jernejp21/VoiceNavi/Hardware/Rev1/Audio Prj.pdf

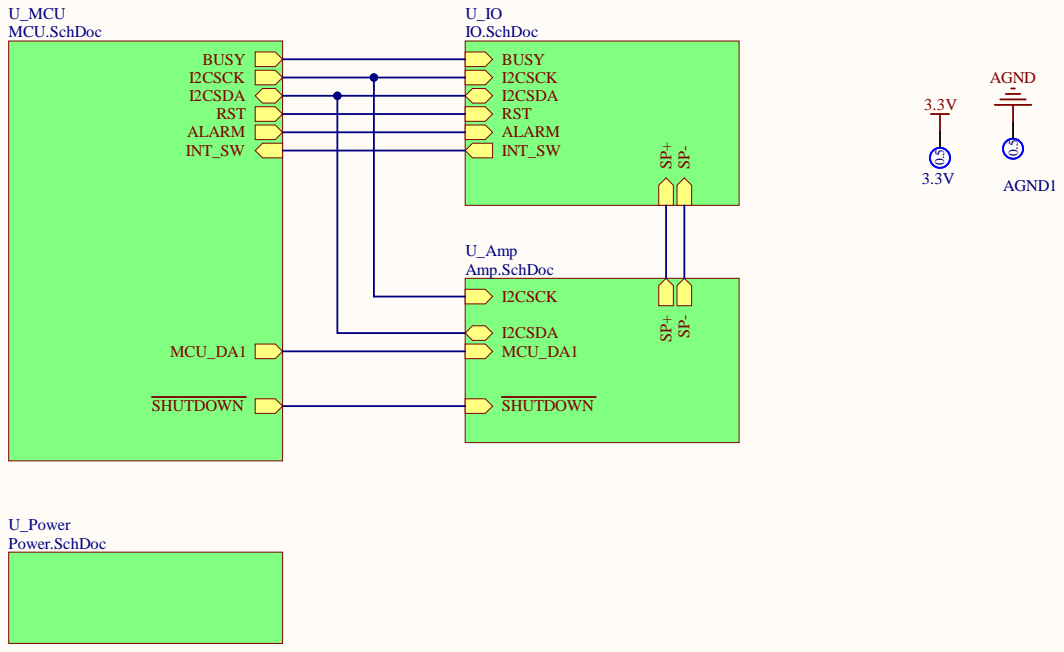
[picture p9: page 1]

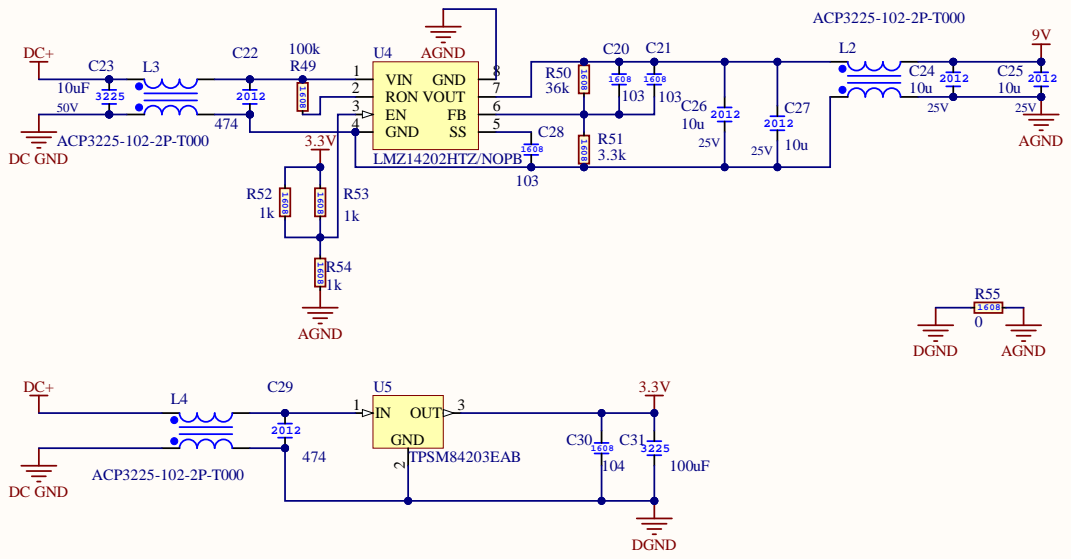
[picture p10: page 2]

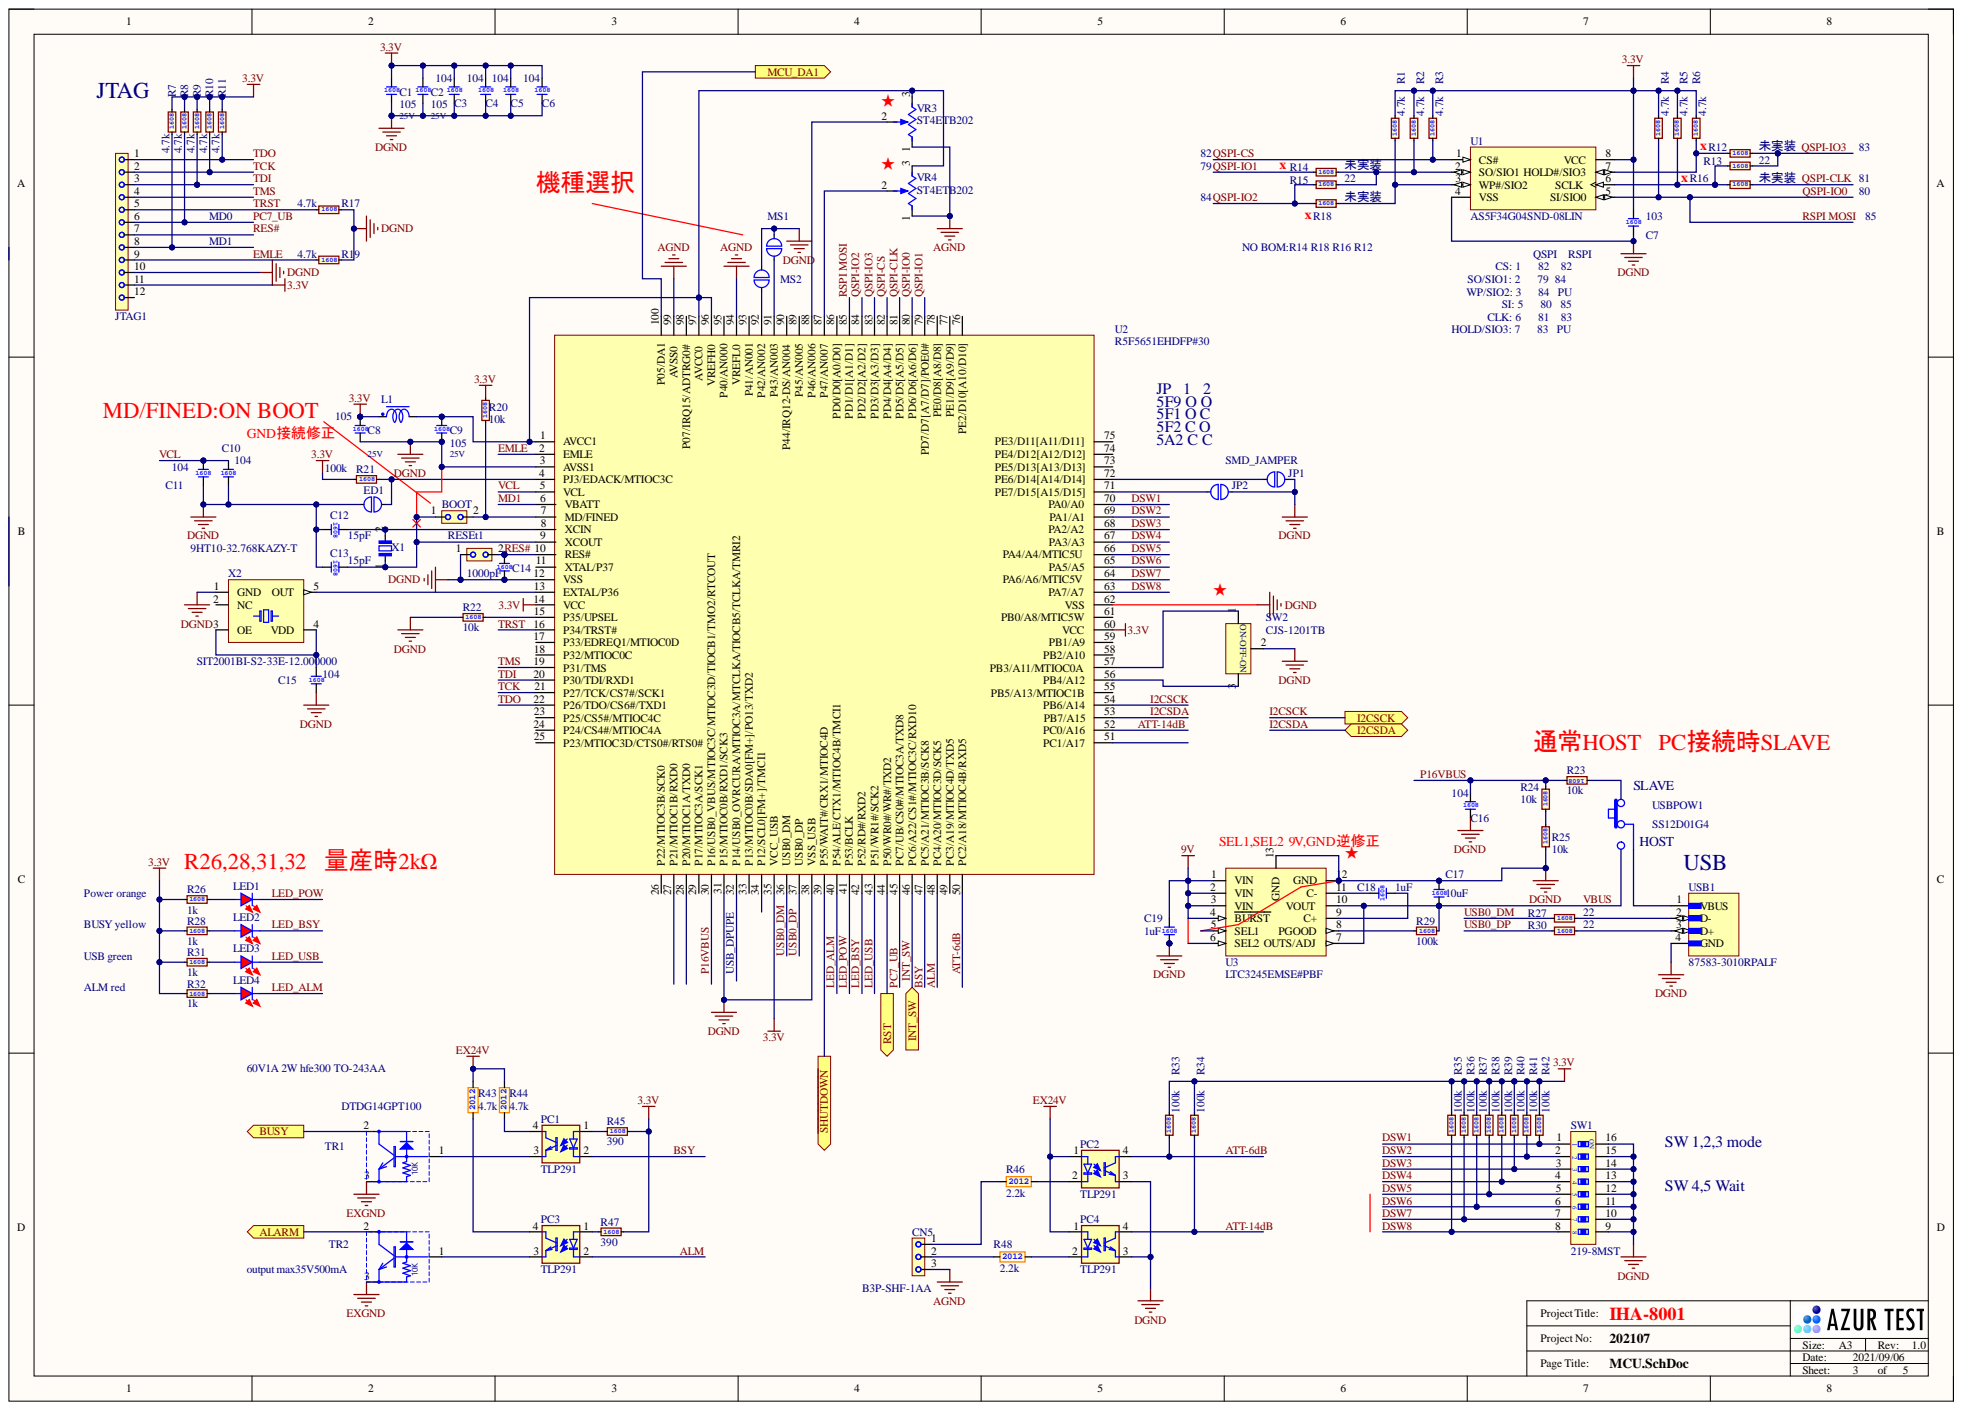
[picture p11: page 3]

MD/FINED:ON BOOT

EMLE | EMLE 2

AVCC1 1

RESEt1 | XCOUT 9
1 | | 2 RES# | RES# 10

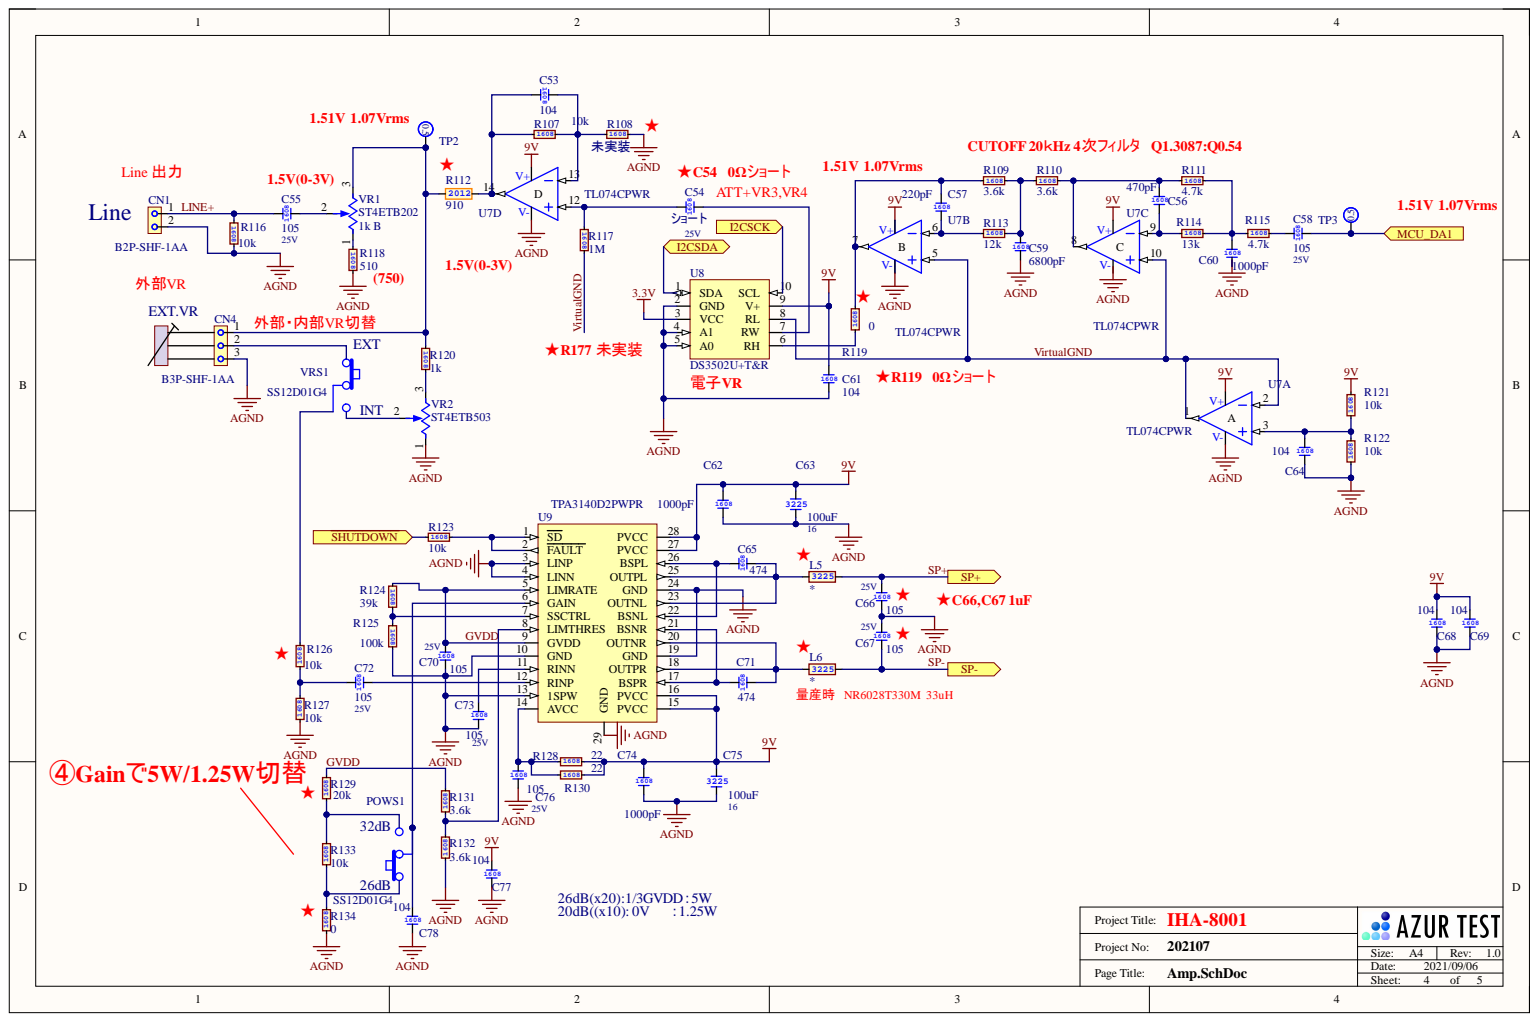
[picture p12: page 4]

SDA 1 | RL
VCC 3 | 8 V+ 9

25V1608 C70 | | LIMTHRES 8

GND 10 | | C71
RINN 11
RINP 12

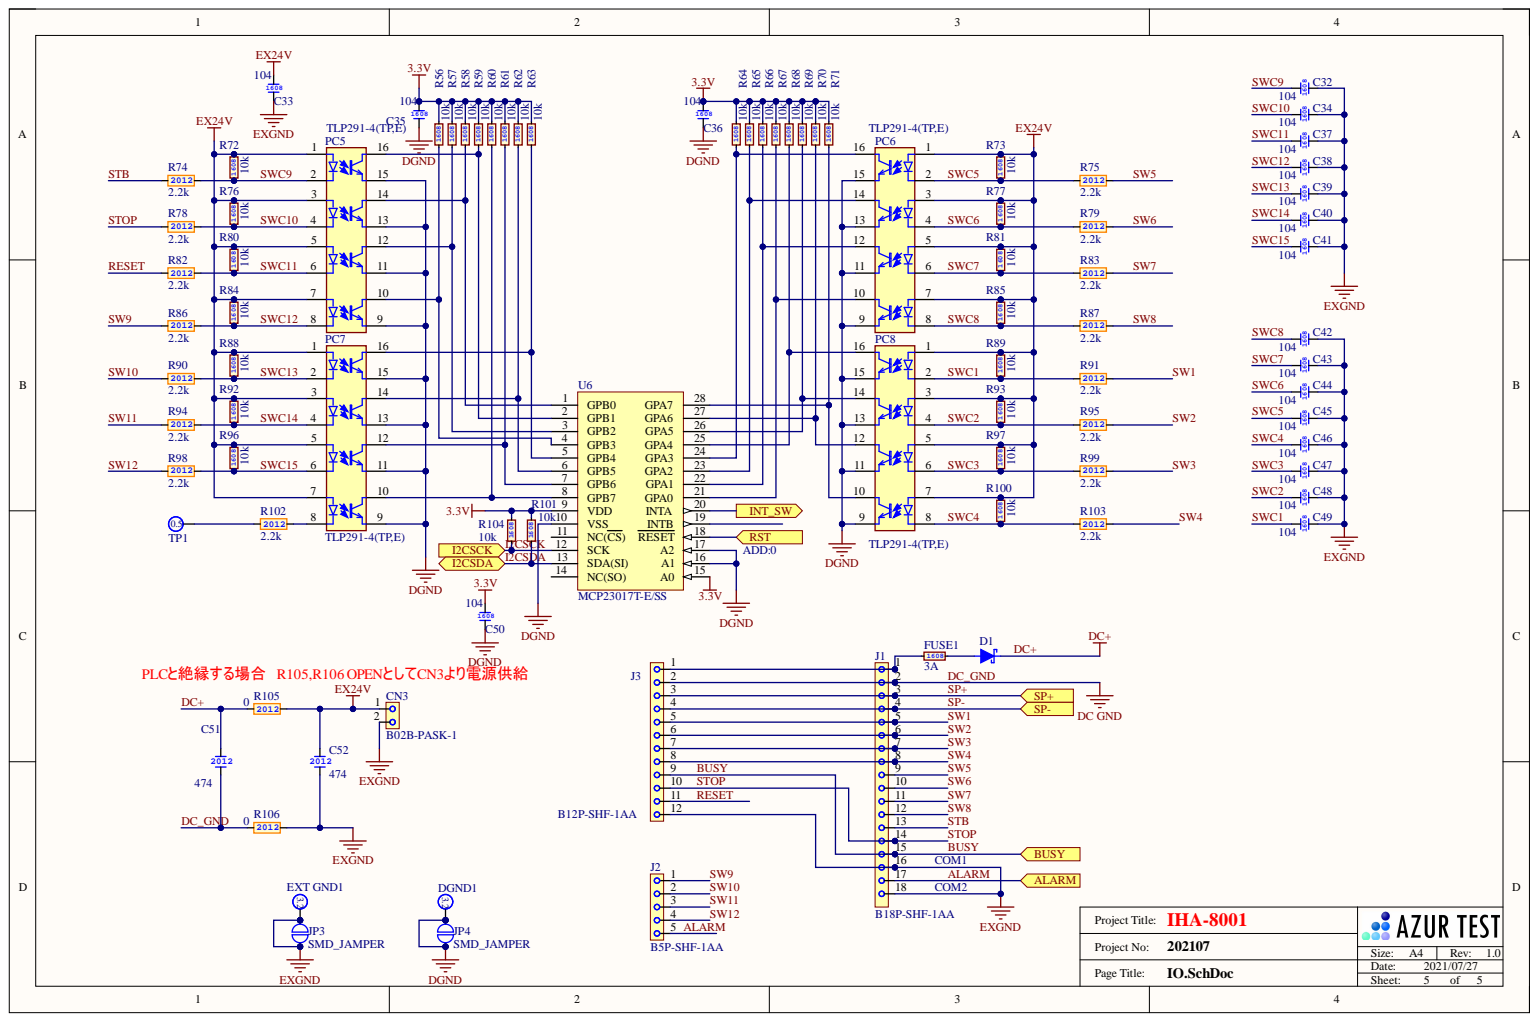
[picture p13: page 5]

3 | 3 SP+
9 BUSY
10 STOP | 10 SW6 BUSY
11 RESET | 11
