jernejp21/VoiceNavi/VoiceNavi/src/smc_gen/PORT_config/PORT_config_user.c

/*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
* Copyright (C) 2019 Renesas Electronics Corporation. All rights reserved.
***********************************************************************************************************************/

/***********************************************************************************************************************
* File Name        : PORT_config_user.c
* Component Version: 2.3.0
* Device(s)        : R5F565N9FxFP
* Description      : This file implements device driver for PORT_config.
***********************************************************************************************************************/

/***********************************************************************************************************************
Pragma directive
***********************************************************************************************************************/
/* Start user code for pragma. Do not edit comment generated here */
/* End user code. Do not edit comment generated here */

/***********************************************************************************************************************
Includes
***********************************************************************************************************************/
#include "r_cg_macrodriver.h"
#include "PORT_config.h"
/* Start user code for include. Do not edit comment generated here */
#include "globals.h"
/* End user code. Do not edit comment generated here */
#include "r_cg_userdefine.h"

/***********************************************************************************************************************
Global variables and functions
***********************************************************************************************************************/
/* Start user code for global. Do not edit comment generated here */
/* End user code. Do not edit comment generated here */

/***********************************************************************************************************************
* Function Name: R_PORT_config_Create_UserInit
* Description  : This function adds user code after initializing PORT
* Arguments    : None
* Return Value : None
***********************************************************************************************************************/

void R_PORT_config_Create_UserInit(void)
{
    /* Start user code for user init. Do not edit comment generated here */
  LED_PowOff();
  LED_BusyOff();
  LED_USBOff();
  LED_AlarmOff();
  PIN_BusySet();
  PIN_AlarmSet();
    /* End user code. Do not edit comment generated here */
}

/* Start user code for adding. Do not edit comment generated here */
void LED_BusyOn()
{
  PORT5.PODR.BIT.B2 = 0;
}

void LED_BusyOff()
{
  PORT5.PODR.BIT.B2 = 1;
}

void LED_BusyToggle()
{
  PORT5.PODR.BIT.B2 ^= 1;
}

void LED_PowOn()
{
  PORT5.PODR.BIT.B3 = 0;
}

void LED_PowOff()
{
  PORT5.PODR.BIT.B3 = 1;
}

void LED_USBOn()
{
  PORT5.PODR.BIT.B1 = 0;
}

void LED_USBOff()
{
  PORT5.PODR.BIT.B1 = 1;
}

void LED_USBToggle()
{
  PORT5.PODR.BIT.B1 ^= 1;
}

void LED_AlarmOn()
{
  PORT5.PODR.BIT.B4 = 0;
}

void LED_AlarmOff()
{
  PORT5.PODR.BIT.B4 = 1;
}

void LED_AlarmToggle()
{
  PORT5.PODR.BIT.B4 ^= 1;
}

uint8_t DIP_ReadState()
{
  //Negative logic, chage to positive.
  return (PORTA.PIDR.BYTE ^ 0xFF);
}

modeSelect_t PIN_BoardSelection()
{
  modeSelect_t ret;
  ret = PORT4.PIDR.BIT.B3; //MS2
  ret |= (PORT4.PIDR.BIT.B2 << 1); //MS1

  return ret;
}

void PIN_ShutdownSet()
{
  PORT5.PODR.BIT.B5 = 1;
}

void PIN_ShutdownReset()
{
  PORT5.PODR.BIT.B5 = 0;
}

void PIN_RstSet()
{
  PORT5.PODR.BIT.B0 = 1;
}

void PIN_RstReset()
{
  PORT5.PODR.BIT.B0 = 0;
}

void PIN_BusySet()
{
  PORTC.PODR.BIT.B5 = 1;
}

void PIN_BusyReset()
{
  PORTC.PODR.BIT.B5 = 0;
}

void PIN_AlarmSet()
{
  PORTC.PODR.BIT.B4 = 1;
}

void PIN_AlarmReset()
{
  PORTC.PODR.BIT.B4 = 0;
}

uint8_t PIN_Get6dB()
{
  return PORTC.PIDR.BIT.B2;
}

uint8_t PIN_Get14dB()
{
  return PORTC.PIDR.BIT.B0;
}

uint8_t PIN_GetExtIRQ()
{
  return PORTC.PIDR.BIT.B6;
}

uint8_t PIN_GetSW2()
{
  // When switch is in middle position, pin status is HIGH.
  // When switch is in voice position, PB3 is LOW.
  // When switch is in chime position, PB4 is LOW.
  // XOR bits to get positive logic - if voice (pos 3), result is 1; if chime (pos 1), result is 2
  uint8_t port = ((PORTB.PIDR.BIT.B4 << 1) | PORTB.PIDR.BIT.B3) ^ 3;
  return port;
}

uint8_t PIN_GetDebugMode()
{
  return PORTE.PIDR.BIT.B6;
}

/* End user code. Do not edit comment generated here */
