jernejp21/VoiceNavi/VoiceNavi/src/play_modes.c

/**
 * Voice Navi Firmware
 *
 * MIT License
 *
 * Copyright (c) 2022 Azurtest
 *
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
 * THE SOFTWARE IS PROVIDED "AS IS", WITHOUT WARRANTY OF ANY KIND, EXPRESS OR
 * IMPLIED, INCLUDING BUT NOT LIMITED TO THE WARRANTIES OF MERCHANTABILITY,
 * FITNESS FOR A PARTICULAR PURPOSE AND NONINFRINGEMENT. IN NO EVENT SHALL THE
 * AUTHORS OR COPYRIGHT HOLDERS BE LIABLE FOR ANY CLAIM, DAMAGES OR OTHER
 * LIABILITY, WHETHER IN AN ACTION OF CONTRACT, TORT OR OTHERWISE, ARISING FROM,
 * OUT OF OR IN CONNECTION WITH THE SOFTWARE OR THE USE OR OTHER DEALINGS IN THE
 * SOFTWARE.
 */

#include "globals.h"

#define STOP 0x01
#define STB 0x02

static uint16_t gpio_prev = 255;
static uint16_t gpioa_prev;
static uint16_t gpiob_prev;

static uint8_t prev_sw = 255;
static uint8_t prev_nr_sw_pressed;
static uint8_t isPrevStop;

static uint8_t bitOrder(uint8_t order)
{
  uint8_t new_order = 0;

  order ^= 0xFF;  //Reverse all bits, to show only active gpios (unpressed state).

  new_order = order >> 4;
  new_order |= (order & 0x01) << 7;
  new_order |= (order & 0x02) << 5;
  new_order |= (order & 0x04) << 3;
  new_order |= (order & 0x08) << 1;

  return new_order;
}

static uint8_t switchToPlay(uint32_t bitField, uint8_t *sw_array_p)
{
//Return value is number of switches pressed
  uint8_t cnt = 0;

  for(int index = 0; index < g_systemStatus.nr_of_switches; index++)
  {
    if(bitField & 1)
    {
      *(sw_array_p + index) = 1;
      cnt++;
    }

    bitField = bitField >> 1;
  }

  return cnt;
}

void emptyPlay(uint8_t *i2c_gpio)
{

}

void normalPlay(uint8_t *i2c_gpio)
{
  uint8_t _gpioa;
  uint8_t _gpiob;
  uint16_t _gpio;
  uint8_t lowestSwitch = 255;
  uint8_t _sw_pressed[MAX_NR_OF_SWITCHES] = {0};
  int isPlayable = 0;
  int isSongChosen = 0;
  uint8_t _nr_sw_pressed;

  /* Check for switch status only when triggered */
  if(g_systemStatus.flag_isIRQ)
  {
    /* Correct switches order according to HW design */
    i2c_gpio[0] = bitOrder(i2c_gpio[0]);
    i2c_gpio[1] ^= 0xFF;  //Convert to positive logic.

    _gpioa = gpioa_prev & i2c_gpio[0];
    _gpiob = gpiob_prev & i2c_gpio[1];
    gpioa_prev = i2c_gpio[0];
    gpiob_prev = i2c_gpio[1];

    //Combine gpioa and gpiob. HW dependent.
    _gpio = ((_gpiob & 0x78) << 5) | _gpioa;

    if(0 != (_gpiob & STOP))
    {
      g_systemStatus.flag_isPlaying = 0;
      g_systemStatus.flag_waitForInterval = 0;
      if(isPrevStop == 0)
      {
        prev_sw--;
      }
      isPrevStop = 1;
      ERROR_ClearErrors();
    }
    else if((0 == g_systemStatus.flag_isPlaying) && (0 == g_systemStatus.flag_waitForInterval))
    {
      /* No interrupts. Play only if a song isn't played yet. */
      /* Get pressed positions. */
      _nr_sw_pressed = switchToPlay(_gpio, _sw_pressed);
      isPrevStop = 0;

      for(int8_t sw_pos = 0; sw_pos < g_systemStatus.nr_of_switches; sw_pos++)
      {
        if(_sw_pressed[sw_pos])
        {
          if(isPlayable == 0)
          {
            lowestSwitch = sw_pos;
            isPlayable = 1;
          }

          if(sw_pos > (int8_t)prev_sw)
          {
            prev_sw = sw_pos;
            isSongChosen = 1;
            break;
          }
        }
      }

      if(isSongChosen)
      {
        FIFO_Put(&prev_sw, 1);
      }
      else if(_nr_sw_pressed != 0)
      {
        FIFO_Put(&lowestSwitch, 1);
        prev_sw = lowestSwitch;
      }
    }
  }
  else
  {
    gpioa_prev = 0;
    gpiob_prev = 0;
  }
}

void lastInputInterruptPlay(uint8_t *i2c_gpio)
{
  uint8_t _gpioa;
  uint8_t _gpiob;
  uint16_t _gpio;
  uint8_t _nr_sw_pressed;
  uint8_t _sw_pressed[MAX_NR_OF_SWITCHES] = {0};
  static uint16_t already_pressed_mask = 0xFFFF;

  /* Check for switch status only when triggered */
  if(g_systemStatus.flag_isIRQ)
  {
    /* Correct switches order according to HW design */
    i2c_gpio[0] = bitOrder(i2c_gpio[0]);
    i2c_gpio[1] ^= 0xFF;  //Convert to positive logic.

    _gpioa = gpioa_prev & i2c_gpio[0];
    _gpiob = gpiob_prev & i2c_gpio[1];
    gpioa_prev = i2c_gpio[0];
    gpiob_prev = i2c_gpio[1];

    //Combine gpioa and gpiob. HW dependent.
    _gpio = ((_gpiob & 0x78) << 5) | _gpioa;

    /* Get number of pressed switches and pressed positions. */
    _nr_sw_pressed = switchToPlay(_gpio, _sw_pressed);

    if(0 != (_gpiob & STOP))
    {
      g_systemStatus.flag_isPlaying = 0;
      ERROR_ClearErrors();
    }
    else if(gpio_prev != _gpio)
    {
      if(_nr_sw_pressed > prev_nr_sw_pressed)
      {
        _gpio &= already_pressed_mask;
        switchToPlay(_gpio, _sw_pressed);
        for(char sw_pos = 0; sw_pos < g_systemStatus.nr_of_switches; sw_pos++)
        {
          if(_sw_pressed[sw_pos])
          {
            if(already_pressed_mask & (1 << sw_pos))
            {
              g_systemStatus.flag_isPlaying = 0;
              FIFO_Put(&sw_pos, 1);
              already_pressed_mask &= ~(1 << sw_pos);
              break;
            }
          }
        }
      }
      else
      {
        already_pressed_mask = ~_gpio;
      }
    }
  }
  else
  {
    gpioa_prev = 0;
    gpiob_prev = 0;
    already_pressed_mask = 0xFFFF;
  }
  gpio_prev = _gpio;
  prev_nr_sw_pressed = _nr_sw_pressed;
}

void priorityPlay(uint8_t *i2c_gpio)
{
  uint8_t _gpioa;
  uint8_t _gpiob;
  uint16_t _gpio;
  uint8_t _sw_pressed[MAX_NR_OF_SWITCHES] = {0};

  /* Check for switch status only when triggered */
  if(g_systemStatus.flag_isIRQ)
  {
    /* Correct switches order according to HW design */
    i2c_gpio[0] = bitOrder(i2c_gpio[0]);
    i2c_gpio[1] ^= 0xFF;  //Convert to positive logic.

    _gpioa = gpioa_prev & i2c_gpio[0];
    _gpiob = gpiob_prev & i2c_gpio[1];
    gpioa_prev = i2c_gpio[0];
    gpiob_prev = i2c_gpio[1];

    //Combine gpioa and gpiob. HW dependent.
    _gpio = ((_gpiob & 0x78) << 5) | _gpioa;

    /* Get number of pressed switches and pressed positions. */
    switchToPlay(_gpio, _sw_pressed);

    if(0 != (_gpiob & STOP))
    {
      g_systemStatus.flag_isPlaying = 0;
      ERROR_ClearErrors();
    }
    else
    {
      if(!g_systemStatus.flag_isPlaying)
      {
        prev_sw = 255;
      }

      for(char sw_pos = 0; sw_pos < g_systemStatus.nr_of_switches; sw_pos++)
      {
        if(_sw_pressed[sw_pos])
        {
          if(sw_pos < prev_sw)
          {
            g_systemStatus.flag_isPlaying = 0;
            FIFO_Put(&sw_pos, 1);
            prev_sw = sw_pos;
            break;
          }
        }
      }
    }
  }
  else
  {
    gpioa_prev = 0;
    gpiob_prev = 0;
  }
}

void inputPlay(uint8_t *i2c_gpio)
{
  uint8_t _gpioa;
  uint8_t _gpiob;
  uint16_t _gpio;
  uint8_t lowestSwitch = 255;
  uint8_t _sw_pressed[MAX_NR_OF_SWITCHES] = {0};
  int isPlayable = 0;
  int isSongChosen = 0;
  uint8_t _nr_sw_pressed;

  /* Check for switch status only when triggered */
  if(g_systemStatus.flag_isIRQ)
  {
    /* Correct switches order according to HW design */
    i2c_gpio[0] = bitOrder(i2c_gpio[0]);
    i2c_gpio[1] ^= 0xFF;  //Convert to positive logic.

    _gpioa = gpioa_prev & i2c_gpio[0];
    _gpiob = gpiob_prev & i2c_gpio[1];
    gpioa_prev = i2c_gpio[0];
    gpiob_prev = i2c_gpio[1];

    //Combine gpioa and gpiob. HW dependent.
    _gpio = ((_gpiob & 0x78) << 5) | _gpioa;

    if((_gpio & (1 << prev_sw)) == 0)
    {
      g_systemStatus.flag_isPlaying = 0;
    }
    gpio_prev = _gpio;

    if(0 != (_gpiob & STOP))
    {
      g_systemStatus.flag_isPlaying = 0;
      ERROR_ClearErrors();
      isPrevStop = 1;
    }
    else if((0 == g_systemStatus.flag_isPlaying) && (isPrevStop == 0))
    {
      /* No interrupts. Play only if a song isn't played yet. */
      /* Get pressed positions. */
      _nr_sw_pressed = switchToPlay(_gpio, _sw_pressed);

      for(int8_t sw_pos = 0; sw_pos < g_systemStatus.nr_of_switches; sw_pos++)
      {
        if(_sw_pressed[sw_pos])
        {
          if(isPlayable == 0)
          {
            lowestSwitch = sw_pos;
            isPlayable = 1;
          }

          if(sw_pos > (int8_t)prev_sw)
          {
            prev_sw = sw_pos;
            isSongChosen = 1;
            break;
          }
        }
      }

      if(isSongChosen)
      {
        FIFO_Put(&prev_sw, 1);
      }
      else if(_nr_sw_pressed != 0)
      {
        FIFO_Put(&lowestSwitch, 1);
        prev_sw = lowestSwitch;
      }
    }
  }
  else
  {
    gpioa_prev = 0;
    gpiob_prev = 0;
    g_systemStatus.flag_isPlaying = 0;
    isPrevStop = 0;
  }
}

void binary127ch_negative(uint8_t *i2c_gpio)
{
  uint8_t _gpioa;
  uint8_t _gpiob;

  /* This mode has negative logic */
  if(g_systemStatus.flag_isIRQ)
  {
    /* Correct switches order according to HW design */
    i2c_gpio[0] = bitOrder(i2c_gpio[0]);
    i2c_gpio[0] ^= 0xFF;  //Convert again, to get positive logic
    i2c_gpio[1] ^= 0xFF;  //Convert to positive logic.

    _gpioa = gpioa_prev & i2c_gpio[0];
    _gpiob = gpiob_prev & i2c_gpio[1];
    gpioa_prev = i2c_gpio[0];
    gpiob_prev = i2c_gpio[1];

    if(0 != (_gpiob & STOP))
    {
      g_systemStatus.flag_isPlaying = 0;
      ERROR_ClearErrors();
      FIFO_Reset();
      return;
    }

    if((0 != (_gpiob & STB)) && (prev_sw != (_gpiob & STB)))
    {
      _gpioa &= 0x7F;  //Pass through mask in case of 8-bit value (mistake)
      switch(_gpioa)
      {
        case 0x7F:
          //STOP
          g_systemStatus.flag_isPlaying = 0;
          FIFO_Reset();
          break;

        default:
          //Subtract positive logic from 0x7E to get negative logic
          _gpioa = 0x7E - _gpioa;
          FIFO_Put(&_gpioa, 1);
          break;
      }
      prev_sw = _gpiob & STB;
    }
    else if(0 == (_gpiob & STB))
    {
      prev_sw = 0;
    }
  }
  else
  {
    prev_sw = 0;
    gpiob_prev = 0;
  }
}

void binary250_positive(uint8_t *i2c_gpio)
{
  uint8_t _gpioa;
  uint8_t _gpiob;
  //uint8_t vol_reduction[2] = {0, 1};

  /* This mode has positive logic */
  if(g_systemStatus.flag_isIRQ)
  {
    /* Correct switches order according to HW design */
    i2c_gpio[0] = bitOrder(i2c_gpio[0]);
    i2c_gpio[0] ^= 0xFF;  //Convert again, to get positive logic
    i2c_gpio[1] ^= 0xFF;  //Convert to positive logic.

    _gpioa = gpioa_prev & i2c_gpio[0];
    _gpiob = gpiob_prev & i2c_gpio[1];
    gpioa_prev = i2c_gpio[0];
    gpiob_prev = i2c_gpio[1];

    if(0 != (_gpiob & STOP))
    {
      g_systemStatus.flag_isPlaying = 0;
      ERROR_ClearErrors();
      FIFO_Reset();
      return;
    }

    if((0 != (_gpiob & STB)) && (prev_sw != (_gpiob & STB)))
    {
      switch(_gpioa)
      {
        case 0x00:
          break;
        case 0xFF:
          //STOP
          g_systemStatus.flag_isPlaying = 0;
          FIFO_Reset();
          break;

          //Not in use
        case 0xFE:
        case 0xFD:
        case 0xFC:
        case 0xFB:
          break;

          /* NOT IN USE
           //Full volume
           case 0xFD:
           //Rewrite existing address with 0, and write to next available address.
           vol_reduction[1] = 1;
           g_binary_vol_reduction = 1;
           NAND_UnlockFlash();
           NAND_WriteToFlash(g_binary_vol_reduction_address, 2, vol_reduction);
           NAND_LockFlash();
           g_binary_vol_reduction_address++;
           break;

           //Fifth volume
           case 0xFC:
           vol_reduction[1] = 5;
           g_binary_vol_reduction = 5;
           NAND_UnlockFlash();
           NAND_WriteToFlash(g_binary_vol_reduction_address, 2, vol_reduction);
           NAND_LockFlash();
           g_binary_vol_reduction_address++;
           break;

           //Half volume
           case 0xFB:
           vol_reduction[1] = 2;
           g_binary_vol_reduction = 2;
           NAND_UnlockFlash();
           NAND_WriteToFlash(g_binary_vol_reduction_address, 2, vol_reduction);
           NAND_LockFlash();
           g_binary_vol_reduction_address++;
           break;
           */

        default:
          _gpioa = _gpioa - 1;
          FIFO_Put(&_gpioa, 1);
          break;
      }
      prev_sw = _gpiob & STB;
    }
    else if(0 == (_gpiob & STB))
    {
      prev_sw = 0;
    }
  }
  else
  {
    prev_sw = 0;
    gpiob_prev = 0;
  }
}

void binary250_negative(uint8_t *i2c_gpio)
{
  uint8_t _gpioa;
  uint8_t _gpiob;
  //uint8_t vol_reduction[2] = {0, 1};

  /* This mode has negative logic */
  if(g_systemStatus.flag_isIRQ)
  {
    /* Correct switches order according to HW design */
    i2c_gpio[0] = bitOrder(i2c_gpio[0]);
    i2c_gpio[0] ^= 0xFF;  //Convert again, to get positive logic
    i2c_gpio[1] ^= 0xFF;  //Convert to positive logic.

    _gpioa = gpioa_prev & i2c_gpio[0];
    _gpiob = gpiob_prev & i2c_gpio[1];
    gpioa_prev = i2c_gpio[0];
    gpiob_prev = i2c_gpio[1];

    if(0 != (_gpiob & STOP))
    {
      g_systemStatus.flag_isPlaying = 0;
      ERROR_ClearErrors();
      FIFO_Reset();
      return;
    }

    if((0 != (_gpiob & STB)) && (prev_sw != (_gpiob & STB)))
    {
      switch(_gpioa)
      {
        case 0x00:
          break;
        case 0xFF:
          //STOP
          g_systemStatus.flag_isPlaying = 0;
          FIFO_Reset();
          break;

          //Not in use
        case 0xFE:
        case 0xFD:
        case 0xFC:
        case 0xFB:
          break;

          /* NOT IN USE
           //Full volume
           case 0xFD:
           //Rewrite existing address with 0, and wite to next available address.
           vol_reduction[1] = 1;
           g_binary_vol_reduction = 1;
           NAND_UnlockFlash();
           NAND_WriteToFlash(g_binary_vol_reduction_address, 2, vol_reduction);
           NAND_LockFlash();
           g_binary_vol_reduction_address++;
           break;

           //Fifth volume
           case 0xFC:
           vol_reduction[1] = 5;
           g_binary_vol_reduction = 5;
           NAND_UnlockFlash();
           NAND_WriteToFlash(g_binary_vol_reduction_address, 2, vol_reduction);
           NAND_LockFlash();
           g_binary_vol_reduction_address++;
           break;

           //Half volume
           case 0xFB:
           vol_reduction[1] = 2;
           g_binary_vol_reduction = 2;
           NAND_UnlockFlash();
           NAND_WriteToFlash(g_binary_vol_reduction_address, 2, vol_reduction);
           NAND_LockFlash();
           g_binary_vol_reduction_address++;
           break;
           */

        default:
          //Subtract positive logic from 0xFA to get negative logic
          _gpioa = 0xFA - _gpioa;
          FIFO_Put(&_gpioa, 1);
          break;
      }
      prev_sw = _gpiob & STB;
    }
    else if(0 == (_gpiob & STB))
    {
      prev_sw = 0;
    }
  }
  else
  {
    prev_sw = 0;
    gpiob_prev = 0;
  }
}

void binary255_positive(uint8_t *i2c_gpio)
{
  uint8_t _gpioa;
  uint8_t _gpiob;

  /* This mode has positive logic */
  if(g_systemStatus.flag_isIRQ)
  {
    /* Correct switches order according to HW design */
    i2c_gpio[0] = bitOrder(i2c_gpio[0]);
    i2c_gpio[0] ^= 0xFF;  //Convert again, to get positive logic
    i2c_gpio[1] ^= 0xFF;  //Convert to positive logic.

    _gpioa = gpioa_prev & i2c_gpio[0];
    _gpiob = gpiob_prev & i2c_gpio[1];
    gpioa_prev = i2c_gpio[0];
    gpiob_prev = i2c_gpio[1];

    if(0 != (_gpiob & STOP))
    {
      g_systemStatus.flag_isPlaying = 0;
      ERROR_ClearErrors();
      FIFO_Reset();
      return;
    }

    if((0 != (_gpiob & STB)) && (prev_sw != (_gpiob & STB)))
    {
      switch(_gpioa)
      {
        case 0x00:
          //STOP
          g_systemStatus.flag_isPlaying = 0;
          FIFO_Reset();
          break;

        default:
          _gpioa = _gpioa - 1;
          FIFO_Put(&_gpioa, 1);
          break;
      }
      prev_sw = _gpiob & STB;
    }
    else if(0 == (_gpiob & STB))
    {
      prev_sw = 0;
    }
  }
  else
  {
    prev_sw = 0;
    gpiob_prev = 0;
  }
}

void binary255_negative(uint8_t *i2c_gpio)
{
  uint8_t _gpioa;
  uint8_t _gpiob;

  /* This mode has negative logic */
  if(g_systemStatus.flag_isIRQ)
  {
    /* Correct switches order according to HW design */
    i2c_gpio[0] = bitOrder(i2c_gpio[0]);
    i2c_gpio[0] ^= 0xFF;  //Convert again, to get positive logic
    i2c_gpio[1] ^= 0xFF;  //Convert to positive logic.

    _gpioa = gpioa_prev & i2c_gpio[0];
    _gpiob = gpiob_prev & i2c_gpio[1];
    gpioa_prev = i2c_gpio[0];
    gpiob_prev = i2c_gpio[1];

    if(0 != (_gpiob & STOP))
    {
      g_systemStatus.flag_isPlaying = 0;
      ERROR_ClearErrors();
      FIFO_Reset();
      return;
    }

    if((0 != (_gpiob & STB)) && (prev_sw != (_gpiob & STB)))
    {
      switch(_gpioa)
      {
        case 0xFF:
          //STOP
          g_systemStatus.flag_isPlaying = 0;
          FIFO_Reset();
          break;

        default:
          //Subtract positive logic from 0xFE to get negative logic
          _gpioa = 0xFE - _gpioa;
          FIFO_Put(&_gpioa, 1);
          break;
      }
      prev_sw = _gpiob & STB;
    }
    else if(0 == (_gpiob & STB))
    {
      prev_sw = 0;
    }
  }
  else
  {
    prev_sw = 0;
    gpiob_prev = 0;
  }
}

void binary255_5F9IH(uint8_t *i2c_gpio)
{
  uint8_t _gpioa;
  uint8_t _gpiob;

  /* This mode has negative logic */
  if(g_systemStatus.flag_isIRQ)
  {
    /* Correct switches order according to HW design */
    i2c_gpio[0] = bitOrder(i2c_gpio[0]);
    i2c_gpio[0] ^= 0xFF;  //Convert again, to get positive logic
    i2c_gpio[1] ^= 0xFF;  //Convert to positive logic.

    _gpioa = gpioa_prev & i2c_gpio[0];
    _gpiob = gpiob_prev & i2c_gpio[1];
    gpioa_prev = i2c_gpio[0];
    gpiob_prev = i2c_gpio[1];

    if(0 != (_gpiob & STOP))
    {
      g_systemStatus.flag_isPlaying = 0;
      ERROR_ClearErrors();
      FIFO_Reset();
      return;
    }

    if(g_systemStatus.flag_isPlaying == 0)
    {
      if((0 != (_gpiob & STB)) && (prev_sw != (_gpiob & STB)))
      {
        switch(_gpioa)
        {
          //No STOP command
          case 0xFF:
            break;

          default:
            //Subtract positive logic from 0xFE to get negative logic
            _gpioa = 0xFE - _gpioa;
            FIFO_Put(&_gpioa, 1);
            break;
        }
        prev_sw = _gpiob & STB;
      }
      else if(0 == (_gpiob & STB))
      {
        prev_sw = 0;
      }
    }
  }
  else
  {
    prev_sw = 0;
    gpiob_prev = 0;
  }
}

void lastInputInterruptPlay_5F9IH(uint8_t *i2c_gpio)
{
  uint8_t _gpioa;
  uint8_t _gpiob;
  uint16_t _gpio;
  uint8_t _nr_sw_pressed;
  uint8_t _sw_pressed[MAX_NR_OF_SWITCHES] = {0};
  static uint16_t already_pressed_mask = 0xFFFF;

  /* Check for switch status only when triggered */
  if(g_systemStatus.flag_isIRQ)
  {
    /* Correct switches order according to HW design */
    i2c_gpio[0] = bitOrder(i2c_gpio[0]);
    i2c_gpio[1] ^= 0xFF;  //Convert to positive logic.

    _gpioa = gpioa_prev & i2c_gpio[0];
    _gpiob = gpiob_prev & i2c_gpio[1];
    gpioa_prev = i2c_gpio[0];
    gpiob_prev = i2c_gpio[1];

    //Combine gpioa and gpiob. HW dependent.
    _gpio = ((_gpiob & 0x78) << 5) | _gpioa;

    /* Get number of pressed switches and pressed positions. */
    _nr_sw_pressed = switchToPlay(_gpio, _sw_pressed);

    if(0 != (_gpiob & STOP))
    {
      g_systemStatus.flag_isPlaying = 0;
      ERROR_ClearErrors();
    }
    else if(gpio_prev != _gpio)
    {
      if(_nr_sw_pressed > prev_nr_sw_pressed)
      {
        _gpio &= already_pressed_mask;
        switchToPlay(_gpio, _sw_pressed);
        for(char sw_pos = 0; sw_pos < g_systemStatus.nr_of_switches; sw_pos++)
        {
          if(_sw_pressed[sw_pos])
          {
            if(already_pressed_mask & (1 << sw_pos))
            {
              if((g_systemStatus.flag_isPlaying == 0) || (prev_sw != sw_pos))
              {
                g_systemStatus.flag_isPlaying = 0;
                FIFO_Put(&sw_pos, 1);
                prev_sw = sw_pos;
                already_pressed_mask &= ~(1 << sw_pos);
                break;
              }
            }
          }
        }
      }
      else
      {
        already_pressed_mask = ~_gpio;
      }
    }
  }
  else
  {
    gpioa_prev = 0;
    gpiob_prev = 0;
    already_pressed_mask = 0xFFFF;
  }
  gpio_prev = _gpio;
  prev_nr_sw_pressed = _nr_sw_pressed;
}
