jernejp21/VoiceNavi/VoiceNavi/src/smc_gen/general/r_smc_interrupt.h

/*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
* Copyright (C) 2019 Renesas Electronics Corporation. All rights reserved.
***********************************************************************************************************************/

/***********************************************************************************************************************
* File Name        : r_smc_interrupt.h
* Version          : 1.2.10
* Device(s)        : R5F565N9FxFP
* Description      : This file implements interrupt setting.
***********************************************************************************************************************/

#ifndef SMC_INTERRUPT_H
#define SMC_INTERRUPT_H

/***********************************************************************************************************************
Macro definitions (Register bit)
***********************************************************************************************************************/

/* Priority level of interrupt source. 
 * These macro definitions are used to set the IPR register directly
 */
#define _00_ICU_PRIORITY_LEVEL0                    (0x00U) /* Level 0 (disabled)  */
#define _01_ICU_PRIORITY_LEVEL1                    (0x01U) /* Level 1  */
#define _02_ICU_PRIORITY_LEVEL2                    (0x02U) /* Level 2  */
#define _03_ICU_PRIORITY_LEVEL3                    (0x03U) /* Level 3  */
#define _04_ICU_PRIORITY_LEVEL4                    (0x04U) /* Level 4  */
#define _05_ICU_PRIORITY_LEVEL5                    (0x05U) /* Level 5  */
#define _06_ICU_PRIORITY_LEVEL6                    (0x06U) /* Level 6  */
#define _07_ICU_PRIORITY_LEVEL7                    (0x07U) /* Level 7  */
#define _08_ICU_PRIORITY_LEVEL8                    (0x08U) /* Level 8  */
#define _09_ICU_PRIORITY_LEVEL9                    (0x09U) /* Level 9  */
#define _0A_ICU_PRIORITY_LEVEL10                   (0x0AU) /* Level 10  */
#define _0B_ICU_PRIORITY_LEVEL11                   (0x0BU) /* Level 11  */
#define _0C_ICU_PRIORITY_LEVEL12                   (0x0CU) /* Level 12  */
#define _0D_ICU_PRIORITY_LEVEL13                   (0x0DU) /* Level 13  */
#define _0E_ICU_PRIORITY_LEVEL14                   (0x0EU) /* Level 14  */
#define _0F_ICU_PRIORITY_LEVEL15                   (0x0FU) /* Level 15  */

/***********************************************************************************************************************
Macro definitions
***********************************************************************************************************************/
/* The macro definitions below list the full set of priority levels as selected in the Interrupts tab
 * Please do not modify this file manually
 */
#define ICU_BSC_BUSERR_PRIORITY                    (_0F_ICU_PRIORITY_LEVEL15)
#define ICU_RAM_RAMERR_PRIORITY                    (_0F_ICU_PRIORITY_LEVEL15)
#define ICU_FCU_FIFERR_PRIORITY                    (_0F_ICU_PRIORITY_LEVEL15)
#define ICU_FCU_FRDYI_PRIORITY                     (_0F_ICU_PRIORITY_LEVEL15)
#define ICU_ICU_SWINT2_PRIORITY                    (_03_ICU_PRIORITY_LEVEL3)
#define ICU_ICU_SWINT_PRIORITY                     (_03_ICU_PRIORITY_LEVEL3)
#define ICU_CMT0_CMI0_PRIORITY                     (_0F_ICU_PRIORITY_LEVEL15)
#define ICU_CMT1_CMI1_PRIORITY                     (_0F_ICU_PRIORITY_LEVEL15)
#define ICU_CMTW0_CMWI0_PRIORITY                   (_0F_ICU_PRIORITY_LEVEL15)
#define ICU_CMTW1_CMWI1_PRIORITY                   (_0F_ICU_PRIORITY_LEVEL15)
#define ICU_USB0_D0FIFO0_PRIORITY                  (_0F_ICU_PRIORITY_LEVEL15)
#define ICU_USB0_D1FIFO0_PRIORITY                  (_0F_ICU_PRIORITY_LEVEL15)
#define ICU_RSPI0_SPRI0_PRIORITY                   (_03_ICU_PRIORITY_LEVEL3)
#define ICU_RSPI0_SPTI0_PRIORITY                   (_03_ICU_PRIORITY_LEVEL3)
#define ICU_RSPI1_SPRI1_PRIORITY                   (_03_ICU_PRIORITY_LEVEL3)
#define ICU_RSPI1_SPTI1_PRIORITY                   (_03_ICU_PRIORITY_LEVEL3)
#define ICU_QSPI_SPRI_PRIORITY                     (_0F_ICU_PRIORITY_LEVEL15)
#define ICU_QSPI_SPTI_PRIORITY                     (_0F_ICU_PRIORITY_LEVEL15)
#define ICU_SDHI_SBFAI_PRIORITY                    (_0F_ICU_PRIORITY_LEVEL15)
#define ICU_MMCIF_MBFAI_PRIORITY                   (_0F_ICU_PRIORITY_LEVEL15)
#define ICU_RIIC1_RXI1_PRIORITY                    (_0F_ICU_PRIORITY_LEVEL15)
#define ICU_RIIC1_TXI1_PRIORITY                    (_0F_ICU_PRIORITY_LEVEL15)
#define ICU_RIIC0_RXI0_PRIORITY                    (_0F_ICU_PRIORITY_LEVEL15)
#define ICU_RIIC0_TXI0_PRIORITY                    (_0F_ICU_PRIORITY_LEVEL15)
#define ICU_RIIC2_RXI2_PRIORITY                    (_0F_ICU_PRIORITY_LEVEL15)
#define ICU_RIIC2_TXI2_PRIORITY                    (_0F_ICU_PRIORITY_LEVEL15)
#define ICU_SCI0_RXI0_PRIORITY                     (_0F_ICU_PRIORITY_LEVEL15)
#define ICU_SCI0_TXI0_PRIORITY                     (_0F_ICU_PRIORITY_LEVEL15)
#define ICU_SCI1_RXI1_PRIORITY                     (_0F_ICU_PRIORITY_LEVEL15)
#define ICU_SCI1_TXI1_PRIORITY                     (_0F_ICU_PRIORITY_LEVEL15)
#define ICU_SCI2_RXI2_PRIORITY                     (_0F_ICU_PRIORITY_LEVEL15)
#define ICU_SCI2_TXI2_PRIORITY                     (_0F_ICU_PRIORITY_LEVEL15)
#define ICU_ICU_IRQ0_PRIORITY                      (_0F_ICU_PRIORITY_LEVEL15)
#define ICU_ICU_IRQ1_PRIORITY                      (_0F_ICU_PRIORITY_LEVEL15)
#define ICU_ICU_IRQ2_PRIORITY                      (_0F_ICU_PRIORITY_LEVEL15)
#define ICU_ICU_IRQ3_PRIORITY                      (_0F_ICU_PRIORITY_LEVEL15)
#define ICU_ICU_IRQ4_PRIORITY                      (_0F_ICU_PRIORITY_LEVEL15)
#define ICU_ICU_IRQ5_PRIORITY                      (_0F_ICU_PRIORITY_LEVEL15)
#define ICU_ICU_IRQ6_PRIORITY                      (_0F_ICU_PRIORITY_LEVEL15)
#define ICU_ICU_IRQ7_PRIORITY                      (_0F_ICU_PRIORITY_LEVEL15)
#define ICU_ICU_IRQ8_PRIORITY                      (_0F_ICU_PRIORITY_LEVEL15)
#define ICU_ICU_IRQ9_PRIORITY                      (_0F_ICU_PRIORITY_LEVEL15)
#define ICU_ICU_IRQ10_PRIORITY                     (_0F_ICU_PRIORITY_LEVEL15)
#define ICU_ICU_IRQ11_PRIORITY                     (_0F_ICU_PRIORITY_LEVEL15)
#define ICU_ICU_IRQ12_PRIORITY                     (_0F_ICU_PRIORITY_LEVEL15)
#define ICU_ICU_IRQ13_PRIORITY                     (_0F_ICU_PRIORITY_LEVEL15)
#define ICU_ICU_IRQ14_PRIORITY                     (_0F_ICU_PRIORITY_LEVEL15)
#define ICU_ICU_IRQ15_PRIORITY                     (_0F_ICU_PRIORITY_LEVEL15)
#define ICU_SCI3_RXI3_PRIORITY                     (_0F_ICU_PRIORITY_LEVEL15)
#define ICU_SCI3_TXI3_PRIORITY                     (_0F_ICU_PRIORITY_LEVEL15)
#define ICU_SCI4_RXI4_PRIORITY                     (_0F_ICU_PRIORITY_LEVEL15)
#define ICU_SCI4_TXI4_PRIORITY                     (_0F_ICU_PRIORITY_LEVEL15)
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

/***********************************************************************************************************************
Typedef definitions
***********************************************************************************************************************/

/***********************************************************************************************************************
Global functions
***********************************************************************************************************************/
void R_Interrupt_Create(void);
/* Start user code for function. Do not edit comment generated here */
/* End user code. Do not edit comment generated here */
#endif
